boanjo/poseidon/fishfeeder/kicad/fishfeeder.sch

## KiCad design fishfeeder/kicad/fishfeeder.sch (2022-08-10)

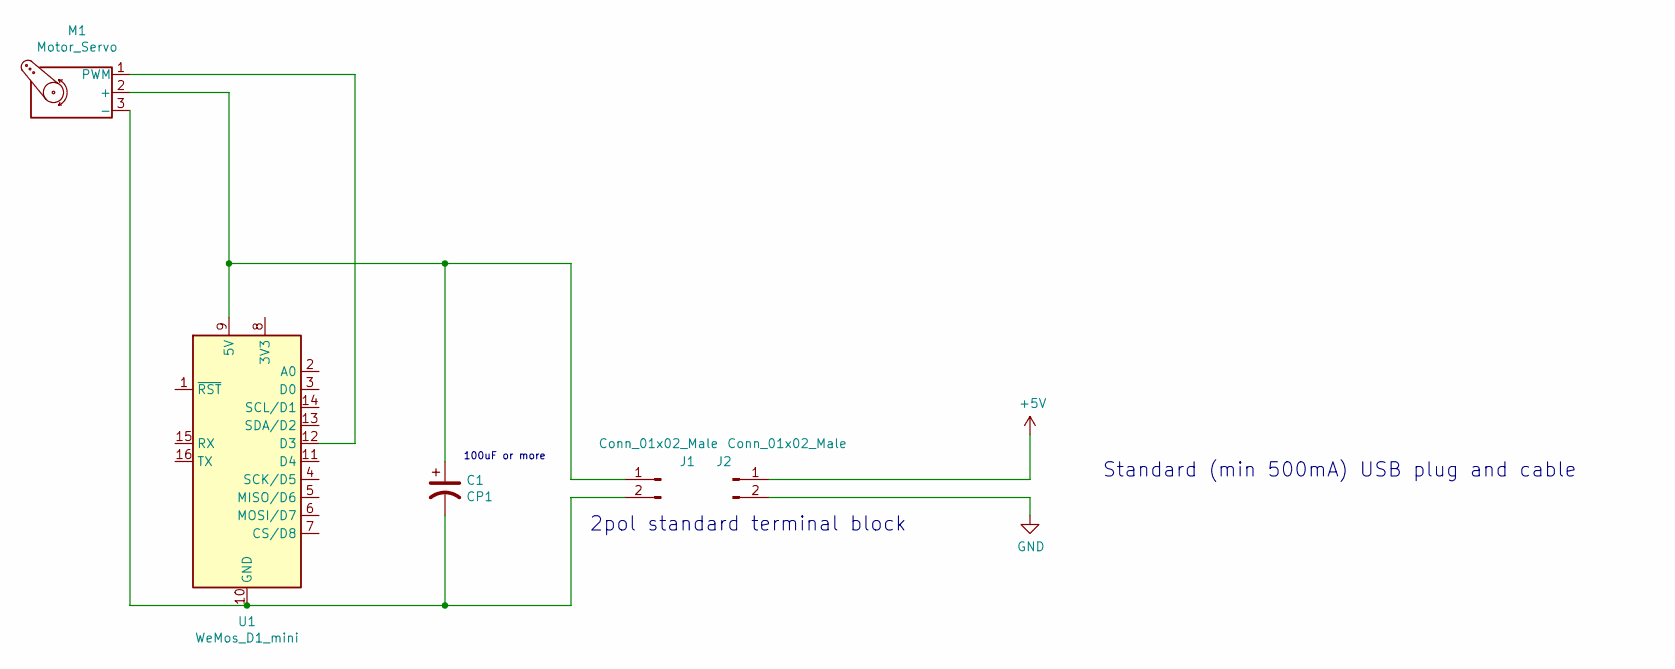
[picture p6: schematic fishfeeder.sch]

Parts:
C1: CP1
J1, J2: Conn_01x02_Male
M1: Motor_Servo
U1: WeMos_D1_mini; WEMOS_D1_mini_light

Connections:
+5V: J2.1
GND: J2.2
unnamed: C1.1, J1.1, M1.2 (+), U1.9 (5V)
unnamed: C1.2, J1.2, M1.3 (-), U1.10 (GND)
unnamed: M1.1 (PWM), U1.12 (D3)

Notes on the sheet:
2pol standard terminal block
Standard (min 500mA) USB plug and cable
100uF or more
