boanjo/poseidon/water_control/kicad/pond control 2.0.sch

## KiCad design water_control/kicad/pond control 2.0.sch (2022-08-10)

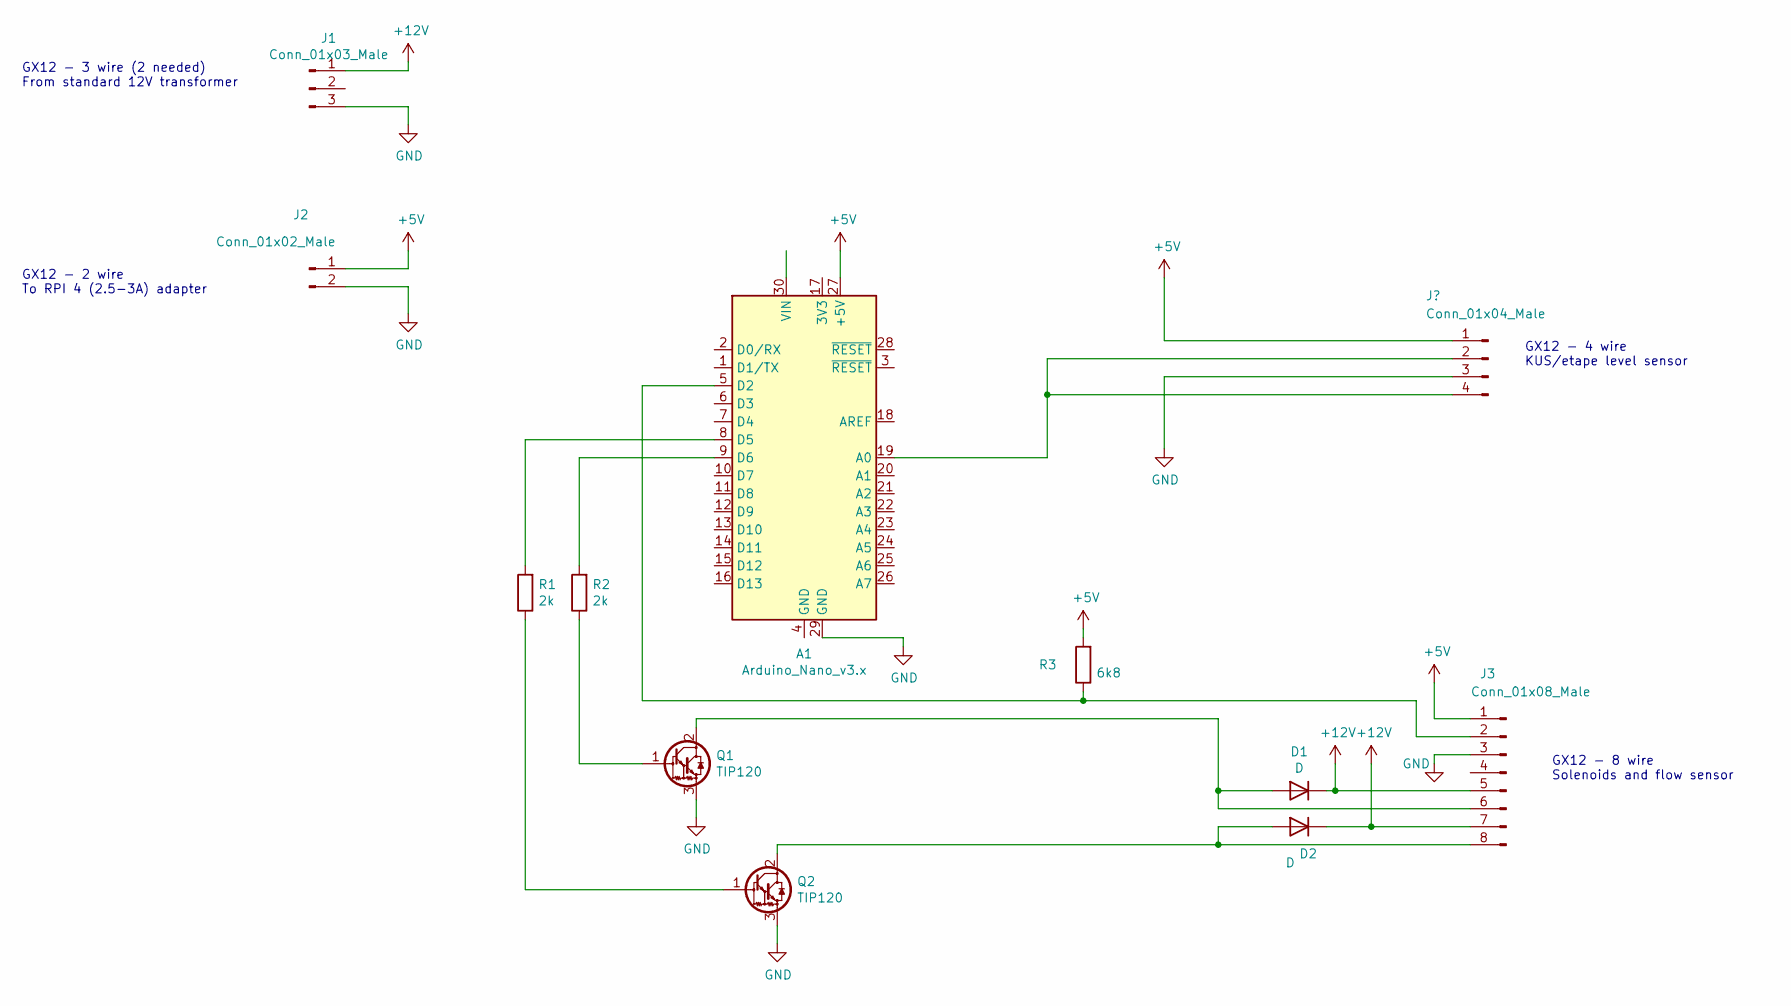
[picture p7: schematic pond control 2.0.sch]

Parts:
A1: Arduino_Nano_v3.x; Arduino_Nano
D1, D2: D
J1: Conn_01x03_Male
J2: Conn_01x02_Male
J3: Conn_01x08_Male
Q1, Q2: TIP120; TO-220-3_Vertical
R1, R2: 2k
R3: 6k8

Connections:
+5V: A1.27 (+5V), J2.1, J3.1, R3.2
+12V: D1.1 (K), D2.1 (K), J1.1, J3.5, J3.7
GND: A1.29 (GND), J1.3, J2.2, J3.3, Q1.3 (E), Q2.3 (E)
unnamed: A1.5 (D2), J3.2, R3.1
unnamed: A1.8 (D5), R1.2
unnamed: A1.9 (D6), R2.2
unnamed: D1.2 (A), J3.6, Q1.2 (C)
unnamed: D2.2 (A), J3.8, Q2.2 (C)
unnamed: Q1.1 (B), R2.1
unnamed: Q2.1 (B), R1.1

Notes on the sheet:
GX12 - 4 wire KUS/etape level sensor
GX12 - 8 wire Solenoids and flow sensor
GX12 - 3 wire (2 needed) From standard 12V transformer
GX12 - 2 wire To RPI 4 (2.5-3A) adapter
